icrashstuff/pico-sunrise/gps.cpp

/**
 * pico-sunrise - A sunrise clock for RP2040 based microcontrollers
 *
 * @file
 * @copyright
 * @parblock
 * SPDX-License-Identifier: MIT
 *
 * SPDX-FileCopyrightText: Copyright (c) 2025 Ian Hangartner <icrashstuff at outlook dot com>
 *
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
 * @brief GPS time synchronization (Implementation)
 */

#include "gps.h"

#include "datetime.h"

#include "hardware/uart.h"
#include "pico/stdlib.h"
#include <stdint.h>
#include <stdio.h>
#include <string.h>

#define arraysizeof(array) (sizeof(array) / sizeof(array[0]))

gps_data_t gps_data = {};

static void gps_handle_character(const uint8_t c);

/**
 * Version of uart_write_blocking() that switches to reading and then handling characters only when the TX FIFO is full
 */
static void gps_uart_write_blocking(uart_inst_t* uart, const uint8_t* src, size_t len)
{
    for (size_t i = 0; i < len; ++i)
    {
        while (!uart_is_writable(uart))
            if (uart_is_readable(uart))
                gps_handle_character(uart_getc(uart));
        uart_get_hw(uart)->dr = *src++;
    }
}

/**
 * Send a NMEA message to the GPS module
 *
 * @param fmt Message data between the message start/end delimiters
 */
static void gps_write_nmea(const char* fmt, ...) __printflike(1, 0);
static void gps_write_nmea(const char* fmt, ...)
{
    const size_t BUF_SIZE = 512;
    char* buf = (char*)calloc(BUF_SIZE, sizeof(char));
    buf[0] = '$';
    buf[1] = '\0';
    va_list args;
    va_start(args, fmt);
    int rc = vsnprintf(buf + strlen(buf), BUF_SIZE - strlen(buf), fmt, args);
    hard_assert(rc >= 0);
    va_end(args);

    uint8_t checksum = 0;
    for (size_t i = 1; i < strlen(buf); i++)
        checksum = checksum ^ buf[i];
    snprintf(buf + strlen(buf), BUF_SIZE - strlen(buf), "*%02X\r\n", checksum);

    /* Flush any data from the RX buffer now */
    while (uart_is_readable(GPS_UART_ID))
        gps_handle_character(uart_getc(GPS_UART_ID));

    gps_uart_write_blocking(GPS_UART_ID, (uint8_t*)buf, strlen(buf));

    /* Flush any data from the RX buffer now */
    while (uart_is_readable(GPS_UART_ID))
        gps_handle_character(uart_getc(GPS_UART_ID));

    free(buf);
}

void gps_set_config()
{
    /* Set update frequency to 2Hz */
    gps_write_nmea("PMTK220,500");

    /* Disable all NMEA sentences except NMEA_SEN_GGA (GPS Fix Data) and NMEA_SEN_ZDA (Time & Date) */
    gps_write_nmea("PMTK314,0,0,0,1,0,0,0,0,0,0,0,0,0,0,0,0,0,1,0");

    /* Query release information */
    gps_write_nmea("PMTK605");
}

void gps_init()
{
    uart_init(GPS_UART_ID, GPS_BAUD_RATE);
    gpio_set_function(GPS_UART_TX_PIN, UART_FUNCSEL_NUM(GPS_UART_ID, GPS_UART_TX_PIN));
    gpio_set_function(GPS_UART_RX_PIN, UART_FUNCSEL_NUM(GPS_UART_ID, GPS_UART_RX_PIN));
    uart_set_format(GPS_UART_ID, GPS_DATA_BITS, GPS_STOP_BITS, GPS_PARITY);
    uart_set_hw_flow(GPS_UART_ID, false, false);
    uart_set_translate_crlf(GPS_UART_ID, 0);

    /* Set update frequency to 1Hz */
    gps_write_nmea("PMTK220,500");

    /* Wait for GPS to send something */
    while (!uart_is_readable(GPS_UART_ID))
    {
        printf("Waiting for GPS to become readable!\n");
        sleep_ms(50);
    }

    gps_data.fix_status = GPS_NO_FIX;

    gps_data.next_config_sync = from_us_since_boot(0);

    gps_set_config();
}

/**
 * Check if a NMEA sentence is valid
 *
 * @param sentence Sentence to check (Must be null terminated)
 * @param len Length of sentence (not including null terminator)
 */
static bool is_valid_nmea_sentence(const char* sentence, size_t len)
{
    if (sentence[0] != '$')
        return false;

    /* Minimum message is "$*00\r\n" */
    if (len < 6)
        return false;

    uint8_t checksum_provided = 0;
    uint8_t checksum_calculated = 0;

    if (sscanf(sentence + len - 5, "*%hhX\r\n", &checksum_provided) != 1)
        return false;

    for (size_t i = 1; i < len - 5; i++)
        checksum_calculated = checksum_calculated ^ sentence[i];

    if (checksum_calculated != checksum_provided)
        return false;

    return true;
}

static void end_of_sentence()
{
    if (!is_valid_nmea_sentence(gps_data.nmea_in_progress, gps_data.nmea_in_progress_len))
    {
        memset(gps_data.nmea_in_progress, 0, sizeof(gps_data.nmea_in_progress));
        gps_data.nmea_in_progress_len = 0;
        return;
    }

    memcpy(gps_data.nmea_last_full, gps_data.nmea_in_progress, sizeof(gps_data.nmea_in_progress));
    gps_data.nmea_last_full_len = gps_data.nmea_in_progress_len;

    memset(gps_data.nmea_in_progress, 0, sizeof(gps_data.nmea_in_progress));
    gps_data.nmea_in_progress_len = 0;

    char* const field_data = (char*)malloc((gps_data.nmea_last_full_len + 4) * sizeof(char));
    char** const argv = (char**)malloc((gps_data.nmea_last_full_len + 4) * sizeof(char*));
    int argc = 0;

    for (size_t i = 0; i < gps_data.nmea_last_full_len; i++)
    {
        switch (gps_data.nmea_last_full[i])
        {
        case '\r':
        case '\n':
            break;
        case '$':
        case ',':
        case '*':
            field_data[i] = '\0';
            field_data[i + 1] = '\0';
            argv[argc++] = field_data + i + 1;
            break;
        default:
            field_data[i] = gps_data.nmea_last_full[i];
            field_data[i + 1] = '\0';
            break;
        }
    }

    if (argc < 1)
    {
        free(field_data);
        free(argv);
        return;
    }

    /* GPGGA - GPS Fix Data
     * 0: ID
     * 1: UTC Time: hhmmss.sss
     * 2: Latitude: ddmm.mmmm
     * 3: Latitude [N: North, S: South]
     * 4: Longitude: ddmm.mmmm
     * 5: Longitude: [E: East, W: West]
     * 6: Fix status: [0: No Fix, 1: Has Fix, 2: Differential GPS Fix]
     * 7: Satellites Used
     * 8: Horizontal dilution of precision
     * 9: Antenna altitude (Mean-sea-level)
     * 10: Antenna altitude Units (Mean-sea-level)
     * 11: Geoidal separation
     * 12: Geoidal separation units
     * 13: Age of differential correction data (seconds) (Empty if no differential data available)
     * 14: Differential station ID (Empty if no differential data available)
     * 15: Checksum
     */
    if (strcmp(argv[0], "GPGGA") == 0 && argc == 16)
    {
        gps_data.fix_status = static_cast<gps_fix_status_t>(strtol(argv[6], NULL, 10));
        gps_data.satellites_used = strtol(argv[7], NULL, 10);
    }

    /* GPZDA - Date & Time
     * 0: ID
     * 1: UTC Time: hhmmss.sss
     * 2: UTC Day
     * 3: UTC Month
     * 4: UTC Year
     * 5: Local zone description (Usually empty)
     * 6: Local zone minutes description (Usually empty)
     * 7: Checksum
     */
    if (strcmp(argv[0], "GPZDA") == 0 && argc == 8)
    {
        datetime_t t = datetime_t(1971, 1, 1);

        sscanf(argv[1], "%02lld%02lld%02lld.%lld", &t.hour, &t.minute, &t.second, &t.microsecond);
        t.microsecond *= 1000;

        t.day = strtol(argv[2], NULL, 10);
        t.month = strtol(argv[3], NULL, 10);
        t.year = strtol(argv[4], NULL, 10);

        set_unix_time(t.to_microseconds_since_1970());
    }

    /* PMTK_DT_RELEASE - Firmware release information
     * 0: ID
     * 1: Release string
     * 2: Build ID
     * 3: Internal use string 1
     * 4: Internal use string 2
     * 5: Checksum
     */
    if (strcmp(argv[0], "PMTK705") == 0 && (argc == 5 || argc == 6))
    {
        strcpy(gps_data.firmware_release_str, argv[1]);
        strcpy(gps_data.firmware_build_id, argv[2]);
        strcpy(gps_data.firmware_internal_1, argv[3]);
        if (argc == 6)
            strcpy(gps_data.firmware_internal_2, argv[4]);
    }

    free(field_data);
    free(argv);
}
#undef SENTENCE_ID_IS

/**
 * Handle a received character
 */
static void gps_handle_character(const uint8_t c)
{
    if (GPS_ECHO)
        stdio_putchar(c);

    if (c == '$')
    {
        memset(gps_data.nmea_in_progress, 0, sizeof(gps_data.nmea_in_progress));
        gps_data.nmea_in_progress_len = 0;
    }

    if (gps_data.nmea_in_progress_len < sizeof(gps_data.nmea_in_progress) - 1)
        gps_data.nmea_in_progress[gps_data.nmea_in_progress_len++] = c;

    if (c == '\n')
        end_of_sentence();
}

void gps_loop()
{
    if (time_reached(gps_data.next_config_sync))
    {
        gps_set_config();
        gps_data.next_config_sync = from_us_since_boot(time_us_64() + MICROSECONDS_PER_SECOND * 5);
    }
    while (uart_is_readable(GPS_UART_ID))
        gps_handle_character(uart_getc(GPS_UART_ID));

    gps_data.watchdog_expiry_time = from_us_since_boot(time_us_64() + WATCHDOG_GPS_TIME * 1000);
    gps_data.perf.end_loop();
}

void gps_thread_func()
{
    gps_init();

    while (1)
    {
        gps_loop();
        sleep_us(1);
    }
}
